aragonxpd154/8-bits-computer/ACC REGISTER/1.0V/PCB/PCB_PCB_ACC Register_2021-10-02.png

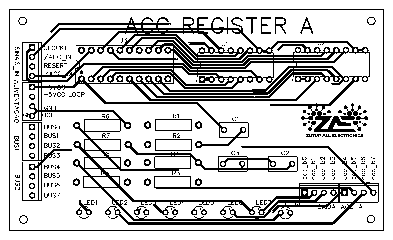
ACC REGISTER/1.0V/PCB/PCB_PCB_ACC Register_2021-10-02.png
