aragonxpd154/8-bits-computer/ACC REGISTER/2.0V/PCB/PCB_PCB_ACC Register 2.0V_2021-10-16.png

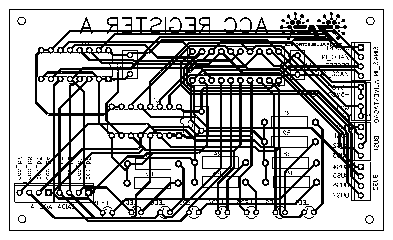
ACC REGISTER/2.0V/PCB/PCB_PCB_ACC Register 2.0V_2021-10-16.png
