aragonxpd154/8-bits-computer/ARITHMETIC LOGIC UNIT/1.0V/PCB/PCB_PCB_Arithmetic Logic Unit_2021-10-05.png

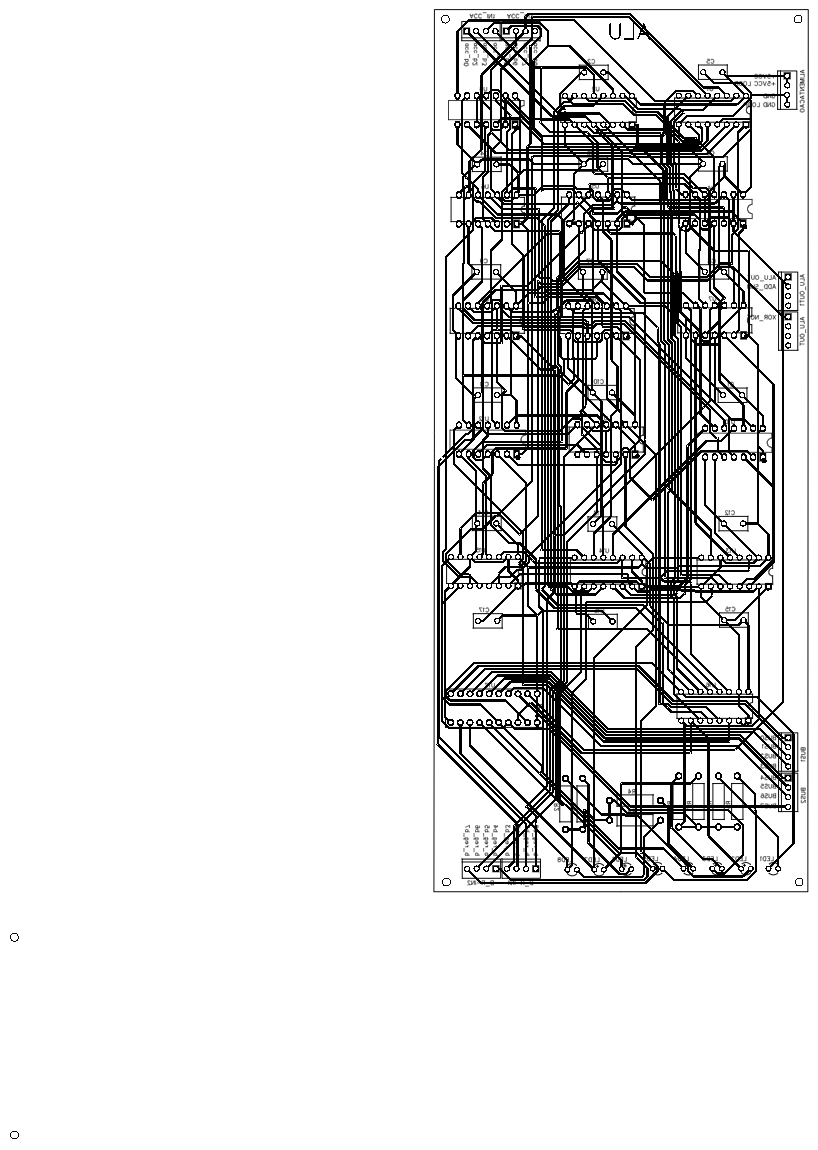
ARITHMETIC LOGIC UNIT/1.0V/PCB/PCB_PCB_Arithmetic Logic Unit_2021-10-05.png
