aragonxpd154/8-bits-computer/ASTABLE AND MONOSTABLE CLOCK CIRCUIT/1.0V/PCB/PCB_PCB_Astavel and Monostable Clock Circuit - 1.0V_2021-10-04.png

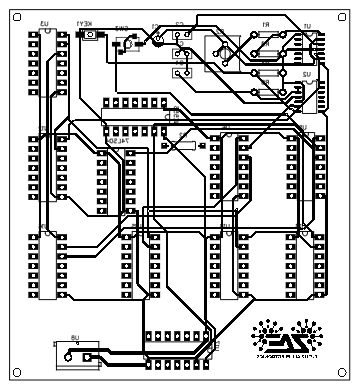
ASTABLE AND MONOSTABLE CLOCK CIRCUIT/1.0V/PCB/PCB_PCB_Astavel and Monostable Clock Circuit - 1.0V_2021-10-04.png
