aragonxpd154/8-bits-computer/DECIMAL DISPLAY/1.0V/PCB/PCB_PCB_Decimal Display_2021-10-08.png

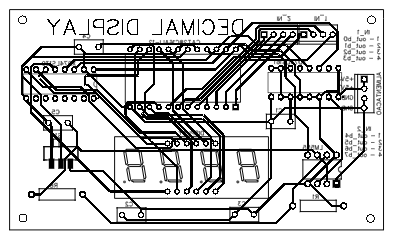
DECIMAL DISPLAY/1.0V/PCB/PCB_PCB_Decimal Display_2021-10-08.png
