aragonxpd154/8-bits-computer/OUTPUT REGISTER/1.0V/PCB/PCB_PCB_Output register_2021-10-31.png

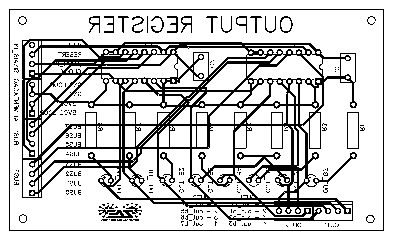
OUTPUT REGISTER/1.0V/PCB/PCB_PCB_Output register_2021-10-31.png
