aragonxpd154/8-bits-computer/PROGRAM COUNTER/1.0V/PCB/PCB_PCB_Program Counter - 1.0_2021-10-28.png

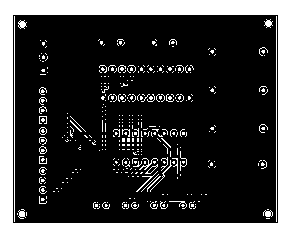
PROGRAM COUNTER/1.0V/PCB/PCB_PCB_Program Counter - 1.0_2021-10-28.png
