aragonxpd154/8-bits-computer/RAM & MAR/1.0V/PCB/PCB_PCB_RAM & MAR - 1.0_2021-12-04.png

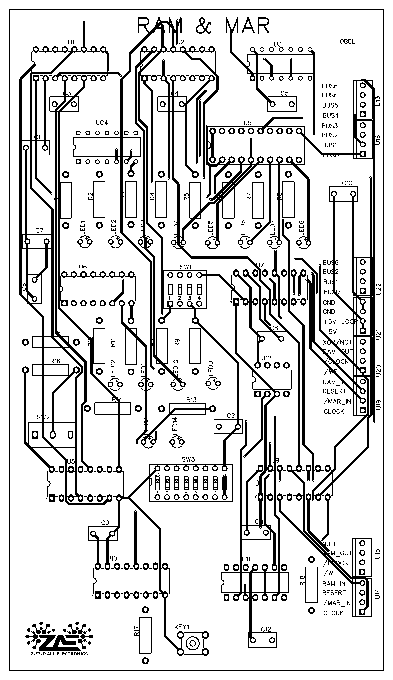
RAM & MAR/1.0V/PCB/PCB_PCB_RAM & MAR - 1.0_2021-12-04.png
