aragonxpd154/8-bits-computer/CONTROL DECODER/1.0V/PCB/BOM_PCB_Control Decoder_2021-12-04.csv

ID | Name | Designator | Footprint | Quantity | Manufacturer Part | Manufacturer | Supplier | Supplier Part | Price | Pins | 3DModel | JLCPCB Part Class | Contributor | link
1 | 100nF 63V poli7 | C1 | CAP-TH_L7.6-W3.8-P5.08-D0.51 | 1 | SR305C105KAR | AVX | LCSC | C444741 | 0.634 | 2 | CAP-TH_L7.6-W3.8-H7.6-P5.08 | Extended Part | LCSC | https://item.szlcsc.com/446097.html
2 | 100nF 63V poli | C2,C3 | CAP-TH_L7.6-W3.8-P5.08-D0.51 | 2 | SR305C105KAR | AVX | LCSC | C444741 | 0.634 | 2 | CAP-TH_L7.6-W3.8-H7.6-P5.08 | Extended Part | LCSC | https://item.szlcsc.com/446097.html
3 | CAT28C16AL-20 | U1,U2,U3 | DIP24-600 | 3 |  |  |  |  |  | 24
4 | SINAIS OUT | U4,U6,U7,U8,U9,U10,U11 | HDR-TH_4P-P2.54-D1.0 | 7 | 171825-4 | TE Connectivity | LCSC | C210162 | 0.156 | 4 | HDR-TH_4P-P2.54-D1.0 | Extended Part | 立创EDA官方封装库 | https://item.szlcsc.com/211174.html
5 | ALIM. | U5 | HDR-TH_4P-P2.54-D1.0 | 1 | 171825-4 | TE Connectivity | LCSC | C210162 | 0.156 | 4 | HDR-TH_4P-P2.54-D1.0 | Extended Part | 立创EDA官方封装库 | https://item.szlcsc.com/211174.html
