aragonxpd154/8-bits-computer/PROGRAM COUNTER/1.0V/PCB/BOM_PCB_Program Counter - 1.0_2021-10-28.csv

ID | Name | Designator | Footprint | Quantity | Manufacturer Part | Manufacturer | Supplier | Supplier Part | Price | Pins | 3DModel | JLCPCB Part Class | Contributor | description | link
1 | 100nF 63V | C1,C2 | CAP-TH_L7.6-W3.8-P5.08-D0.51 | 2 | SR305C105KAR | AVX | LCSC | C444741 | 0.402 | 2 | CAP-TH_L7.6-W3.8-H7.6-P5.08 | Extended Part | LCSC |  | https://item.szlcsc.com/446097.html
2 | VERDE | LED1,LED2,LED3,LED4 | LED-TH_BD3.0-P2.54-RD-GREEN | 4 | 264-7GD | Everlight Elec | LCSC | C605465 | 0.057 | 2 | LED-TH_BD3.0-P2.54-RD-GREEN | Extended Part | 立创EDA官方封装库 |  | https://atta.szlcsc.com/upload/public/pdf/source/20200615/C605465_1C0E18C6C0FE32F26DC47CD74F40D8BE.pdf
3 | 470 | R1,R2,R3,R4 | RES-TH_BD3.0-L9.5-P13.50-D0.6 | 4 | CFR02SJ0823A10 | UniOhm | LCSC | C69876 |  | 2 | RES-TH_BD3.0-L9.5-P13.50-D0.6 |  | 立创EDA官方封装库 |  | https://item.szlcsc.com/59631.html
4 | XD74LS161 | U1 | DIP-16_L19.2-W6.6-P2.54-LS7.6-BL | 1 | XD74LS161 | XINLUDA | LCSC | C609766 | 0.444 | 16 | DIP-16_L19.2-W6.6-H3.3-LS7.62-P2.54 | Extended Part | 立创EDA官方封装库 |  | https://item.szlcsc.com/82841.html
5 | SN74LS245N | U2 | DIP-20_L25.5-W10.0-P2.54-LS7.6-BL | 1 | SN74LS245N | Texas Instruments | LCSC | C352966 | 0.634 | 20 | DIP-20_L25.5-W10.0-H3.7-P2.54-LS7.6-BL | Extended Part | LCSC |  | https://item.szlcsc.com/398272.html
6 | SINAIS IN | U3 | HDR-TH_4P-P2.54-D1.0 | 1 | 171825-4 | TE Connectivity | LCSC | C210162 | 0.156 | 4 | HDR-TH_4P-P2.54-D1.0 | Extended Part | 立创EDA官方封装库 |  | https://item.szlcsc.com/211174.html
7 | 171825-4 | U4 | HDR-TH_4P-P2.54-D1.0 | 1 | 171825-4 | TE Connectivity | LCSC | C210162 | 0.156 | 4 | HDR-TH_4P-P2.54-D1.0 | Extended Part | 立创EDA官方封装库 |  | https://item.szlcsc.com/211174.html
8 | BUS | U5 | HDR-TH_4P-P2.54-D1.0 | 1 | 171825-4 | TE Connectivity | LCSC | C210162 | 0.156 | 4 | HDR-TH_4P-P2.54-D1.0 | Extended Part | 立创EDA官方封装库 |  | https://item.szlcsc.com/211174.html
9 | GS012-3.5-3P | U6 | H3-3.5-11.5X7.0MM | 1 | GS012-3.5-3P |  |  |  |  | 3 |  |  |  | DIP Screw Terminal;
