aragonxpd154/8-bits-computer/ASTABLE AND MONOSTABLE CLOCK CIRCUIT/2.0V/PCB/BOM_PCB_Astavel and Monostable Clock Circuit - 2.0_2021-10-20.csv

ID | Name | Designator | Footprint | Quantity | Manufacturer Part | Manufacturer | Supplier | Supplier Part | Price | Pins | 3DModel | JLCPCB Part Class | Contributor | Resistance(Ohms) | description | link
1 | 10uF 25V TANTALUM | C1 | CAP-TH_BD4.0-P1.50-D0.8-FD | 1 | SK100M035B070A | CapXon | LCSC | C62931 | 0.018 | 2 | CAP-TH_D4.0-H7.0-P1.5 | Extended Part | 官方封装库 |  |  | https://item.szlcsc.com/44342.html
2 | 10nF 63V poli | C2,C3 | CAP-TH_L5.5-W3.0-P5.00-D0.5 | 2 | 0.01uF(103) 100V | ReliaPro | LCSC | C10722 |  | 2 | CAP-TH_L5.5-W3.0-P5.00-D0.5 |  | 立创EDA官方封装库 |  |  | https://lcsc.com/product-detail/Polyester-Film-Capacitors_Made-in-China-0-01uF-103-100V_C10722.html
3 | 330nF 63V poli | C4 | CAP-TH_L5.5-W3.0-P5.00-D0.5 | 1 | 0.01uF(103) 100V | ReliaPro | LCSC | C10722 |  | 2 | CAP-TH_L5.5-W3.0-P5.00-D0.5 |  | 立创EDA官方封装库 |  |  | https://lcsc.com/product-detail/Polyester-Film-Capacitors_Made-in-China-0-01uF-103-100V_C10722.html
4 | 100nF 63V poli | C5,C6,C7 | CAP-TH_L5.5-W3.0-P5.00-D0.5 | 3 | 0.01uF(103) 100V | ReliaPro | LCSC | C10722 |  | 2 | CAP-TH_L5.5-W3.0-P5.00-D0.5 |  | 立创EDA官方封装库 |  |  | https://lcsc.com/product-detail/Polyester-Film-Capacitors_Made-in-China-0-01uF-103-100V_C10722.html
5 | VERDE | OUT | LED-TH_BD3.0-P2.54-RD-GREEN | 1 | 264-7GD | Everlight Elec | LCSC | C605465 | 0.057 | 2 | LED-TH_BD3.0-P2.54-RD-GREEN | Extended Part | 立创EDA官方封装库 |  |  | https://atta.szlcsc.com/upload/public/pdf/source/20200615/C605465_1C0E18C6C0FE32F26DC47CD74F40D8BE.pdf
6 | 150 | R1 | RES-TH_BD3.0-L9.5-P13.50-D0.6 | 1 | 7501/2w5% |  | LCSC | C48642 | 0.003 | 2 | RES-TH_BD3.0-L9.5-P13.50-D0.6 |  | 立创EDA官方封装库 |  |  | https://item.szlcsc.com/59631.html
7 | 10 | R2 | RES-TH_BD3.0-L9.5-P13.50-D0.6 | 1 | 7501/2w5% |  | LCSC | C48642 | 0.003 | 2 | RES-TH_BD3.0-L9.5-P13.50-D0.6 |  | 立创EDA官方封装库 |  |  | https://item.szlcsc.com/59631.html
8 | 10K | R4 | RES-TH_BD3.0-L9.5-P13.50-D0.6 | 1 | 7501/2w5% |  | LCSC | C48642 | 0.003 | 2 | RES-TH_BD3.0-L9.5-P13.50-D0.6 |  | 立创EDA官方封装库 |  |  | https://item.szlcsc.com/59631.html
9 | 330K | R5 | RES-TH_BD3.0-L9.5-P13.50-D0.6 | 1 | 7501/2w5% |  | LCSC | C48642 | 0.003 | 2 | RES-TH_BD3.0-L9.5-P13.50-D0.6 |  | 立创EDA官方封装库 |  |  | https://item.szlcsc.com/59631.html
10 | 470 | R6 | RES-TH_BD3.0-L9.5-P13.50-D0.6 | 1 | 7501/2w5% |  | LCSC | C48642 | 0.003 | 2 | RES-TH_BD3.0-L9.5-P13.50-D0.6 |  | 立创EDA官方封装库 |  |  | https://item.szlcsc.com/59631.html
11 | 100K LINEAR | AJT._FREQ | RES-ADJ-TH_3362P | 1 | 3362P-1-502LF | BOURNS | LCSC | C81260 | 0.203 | 3 | 3362P |  | 立创EDA官方封装库 | 5K |  | https://lcsc.com/product-detail/Precision-Potentiometer_Made-in-China-3362P-1-105_C20063.html
12 | SWITCH-SPDT | S1 | SWITCH-SPDT-SMD | 1 |  |  |  |  |  | 3 |  |  | SparkFun
13 | NE556N | NE556N | DIP-14_L19.0-W7.0-P2.54-LS7.6-BL | 1 | NE556N | TI | LCSC | C66175 | 0.343 | 14 | DIP-14_L19.0-W7.0-H3.5-LS7.62-P2.54 | Extended Part | 立创EDA官方封装库 |  |  | https://item.szlcsc.com/46313.html
14 | GS012-3.5-3P | U4,U5 | H3-3.5-11.5X7.0MM | 2 | GS012-3.5-3P |  |  |  |  | 3 |  |  |  |  | DIP Screw Terminal;
15 | button6*6*8.5 | CLOCK_MANUAL | KEY-TH_4P-L6.0-W6.0-P4.50 | 1 | button6*6*8.5 | ReliaPro | LCSC | C59980 | 0.017 | 4 | KEY-TH_4P-L6.0-W6.0-H4.3-LS6.5-P4.5 |  | 官方封装库 |  |  | https://lcsc.com/product-detail/Tactile-Switches_Made-in-China-Made-in-China-Made-in-China-Made-in-Cina-button6-6-8-5-Straight-line_C59980.html
16 | DM74LS04N | DM74LS04N | DIL-14 | 1 |  |  |  |  |  | 14 |  |  | keyboardjunkie
17 | XD74LS04 | 74LS00 | DIP-14_L19.4-W6.4-P2.54-LS7.6-BL | 1 | XD74LS04 | XINLUDA(信路达) | LCSC | C513524 | 0.234 | 14 | DIP-14_L19.4-W6.4-H5.3-P2.54-LS7.6-BL | Extended Part | LCSC |  |  | https://item.szlcsc.com/639765.html
