aragonxpd154/8-bits-computer/ASTABLE AND MONOSTABLE CLOCK CIRCUIT/1.0V/PCB/BOM_PCB_Astavel and Monostable Clock Circuit - 1.0V_2021-10-04.csv

EU IRIA | Nome | Designador | Pegada | Quantidade | Peça do Fabricante | Fabricante | Fornecedor | Peça do Fornecedor | Preço | Alfinetes | Contributor
1 | RTH025W | R2 | RTH025W | 1 |  |  |  |  |  | 2 | DangerousPrototype
2 | NE556DR | U1,U2 | SOIC-14_150MIL | 2 |  |  |  |  |  | 14
3 | 10 | R1 | AXIAL-0.3 | 1 |  |  |  |  |  | 2
4 | 100k | R2 | RES-ADJ_3386P | 1 |  |  |  |  |  | 3
5 | 10uF | C2 | RAD-0.1 | 1 |  |  |  |  |  | 2
6 | 10uF | C1 | CAP-D3.0XF1.5 | 1 |  |  |  |  |  | 2
7 | RS-285G05A2 | SW3 | KEY-6.0X3.6X2.5MM | 1 |  |  |  |  |  | 4
8 | 10k | R4 | AXIAL-0.3 | 1 |  |  |  |  |  | 2
9 | 150 | R3 | AXIAL-0.3 | 1 |  |  |  |  |  | 2
10 | Switch | KEY1 | KEY-3.0*4.0 | 1 |  |  |  |  |  | 2
11 | 10nF 63V Poliester | C3 | RAD-0.1 | 1 |  |  |  |  |  | 2
12 | 330nF 63V Poliester | C4 | RAD-0.1 | 1 |  |  |  |  |  | 2
13 | 330k | R5 | AXIAL-0.3 | 1 |  |  |  |  |  | 2
14 | 74LS00 | U3,U5,U6,U16 | 74LS04 DIP-14 | 4 |  |  |  |  |  | 14
15 | 74LS04 | U12,U13,U14,U15,U17,74LS04 | 74LS04 DIP-14 | 6 |  |  |  |  |  | 14
16 | NE556 | NE556 | 74LS04 DIP-14 | 1 |  |  |  |  |  | 14
17 | SCREWTERMINAL-5MM-2 | U8 | SCREWTERMINAL-5MM-2 | 1 |  |  |  |  |  | 2 | SparkFun
