aragonxpd154/8-bits-computer/PROGRAM COUNTER/3.0V/PCB/PCB_Program Counter - 3.0_2021-10-28.dxf

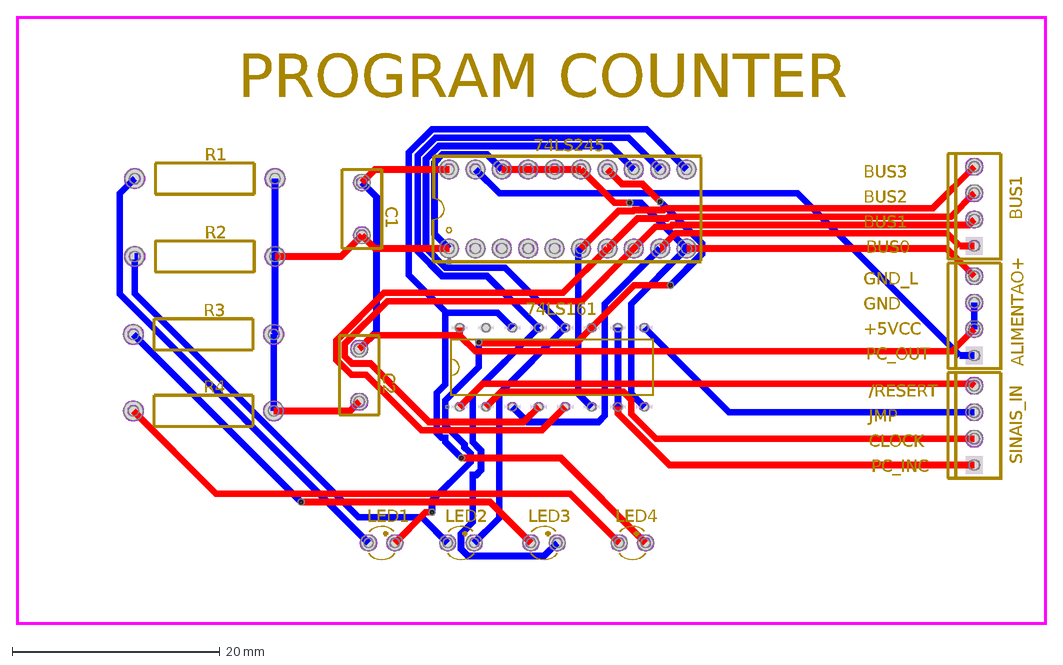
[picture p44: CAD file, 2021-10-28]
PROGRAM COUNTER/3.0V/PCB/PCB_Program Counter - 3.0_2021-10-28.dxf
PC_INC
CLOCK
JMP
/RESERT
PC_OUT
+5VCC
GND
GND_L
BUS0
BUS1
BUS2
BUS3
PROGRAM COUNTER
C1
C2
LED1
LED2
LED3
LED4
R1
R2
R3
R4
74LS161
74LS245
SINAIS_IN
ALIMENTAO+
