aragonxpd154/8-bits-computer/RAM & MAR/1.0V/PCB/PCB_RAM & MAR - 1.0_2021-12-04.dxf

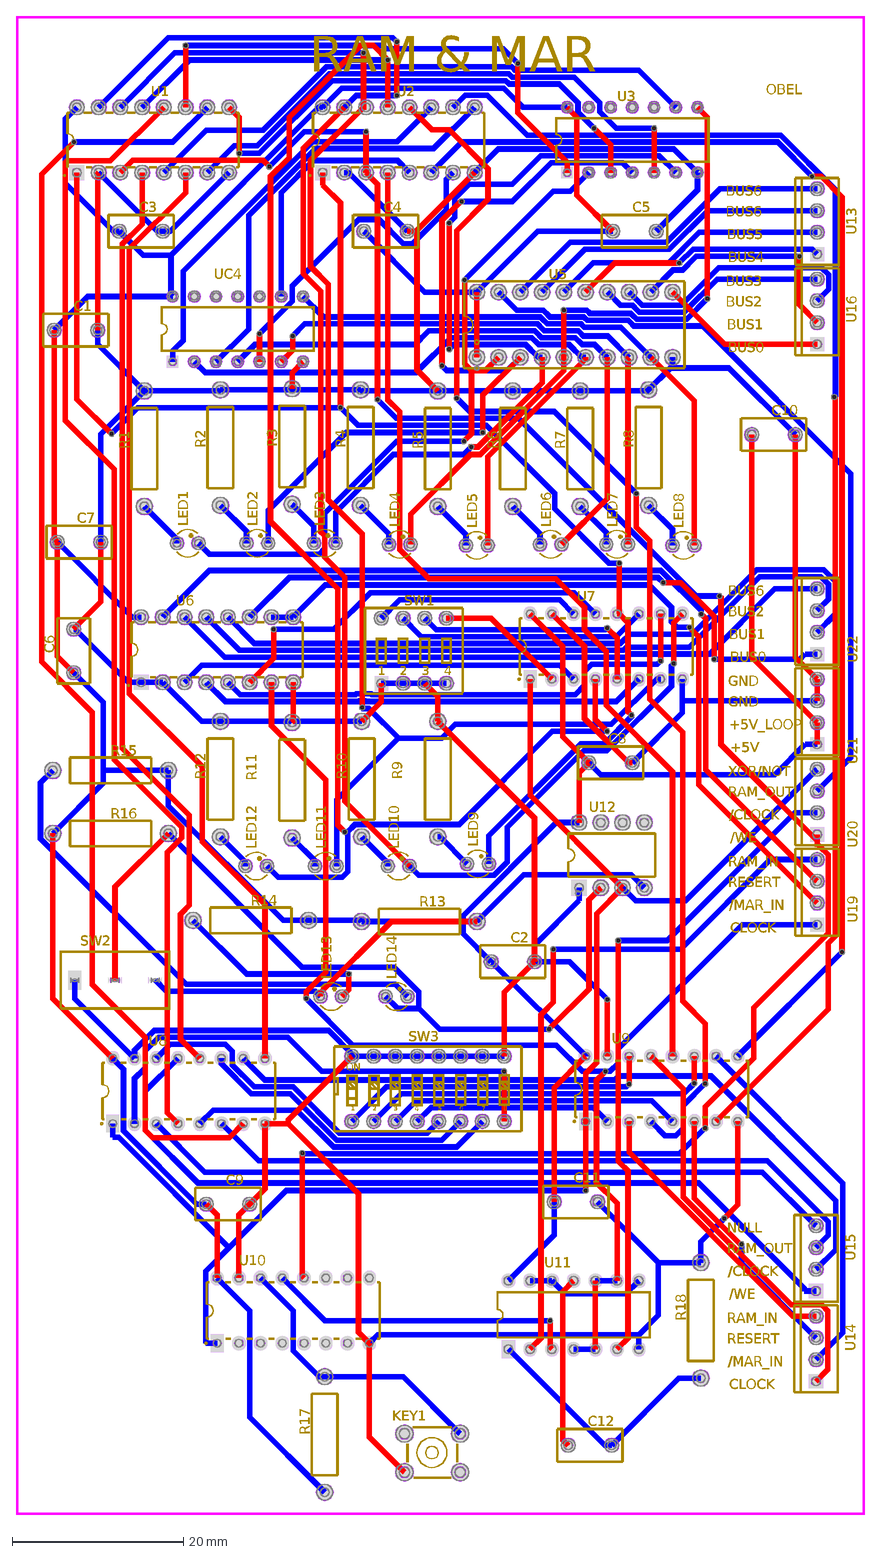
[picture p45: CAD file, 2021-12-04]
RAM & MAR/1.0V/PCB/PCB_RAM & MAR - 1.0_2021-12-04.dxf
OBEL
BUS3
BUS1
BUS0
BUS2
BUS6
BUS4
BUS5
GND
+5V
+5V_LOOP
XOR/NOT
/CLOCK
/WE
RAM_OUT
RESERT
CLOCK
/MAR_IN
RAM_IN
NULL
RAM & MAR
KEY1
LED1
LED2
LED3
LED4
LED5
LED6
LED7
LED8
LED9
LED10
LED11
LED12
LED13
LED14
SW1
1
2
3
4
SW2
SW3
ON
5
6
7
8
U1
U2
U3
U5
U6
U7
U8
U9
U10
U11
U12
U13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
