aragonxpd154/8-bits-computer/INSTRUCTION REGISTER/2.0V/PCB/PCB_PCB_Instruction Register 2.0V_2021-10-21.png

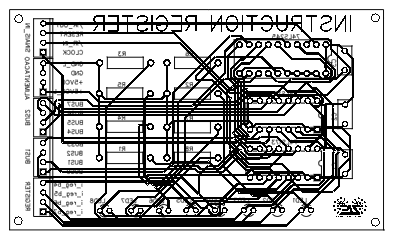
INSTRUCTION REGISTER/2.0V/PCB/PCB_PCB_Instruction Register 2.0V_2021-10-21.png
