aragonxpd154/8-bits-computer/ASTABLE AND MONOSTABLE CLOCK CIRCUIT/1.0V/Schematic_Astavel and Monostable Clock Circuit_2021-10-04.pdf

# U7.1GND

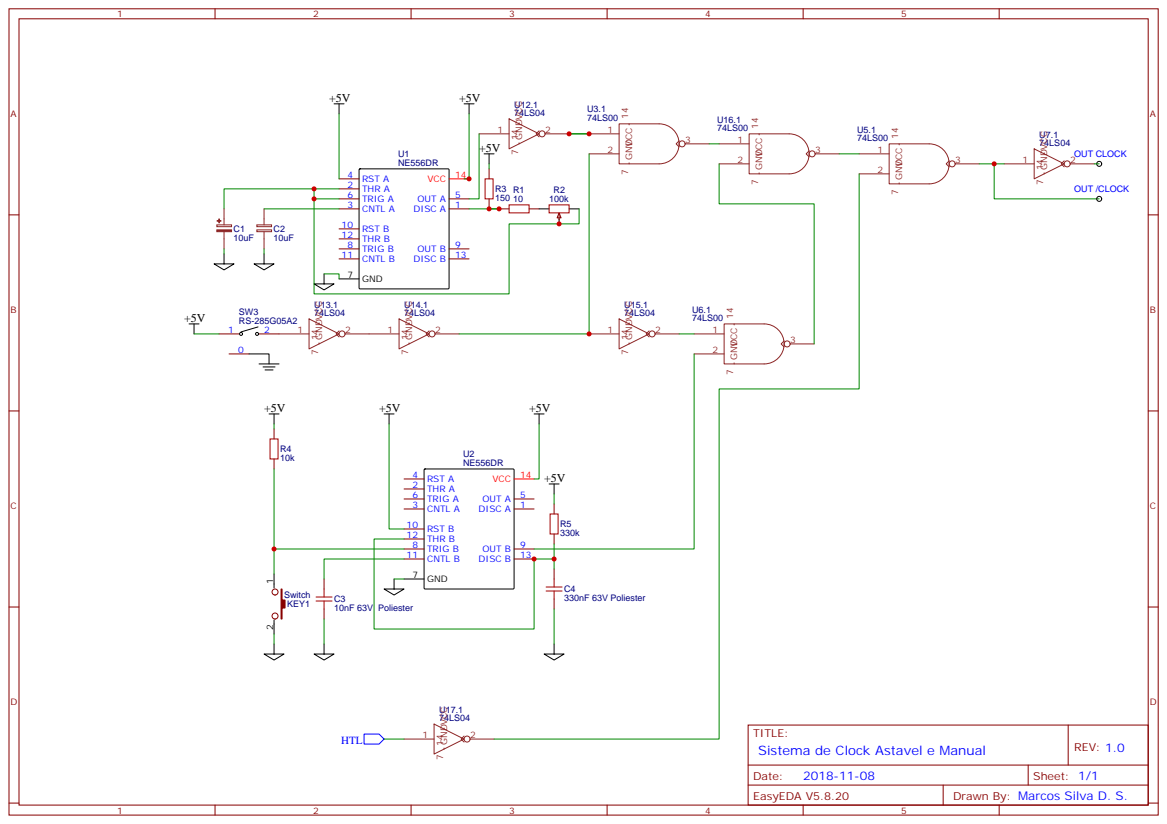
[picture p59: page 1]

TITLE:
Sistema de Clock Astavel e Manual
