aragonxpd154/8-bits-computer/ARITHMETIC LOGIC UNIT/1.0V/Schematic_Arithmetic Logic Unit_2021-10-03.pdf

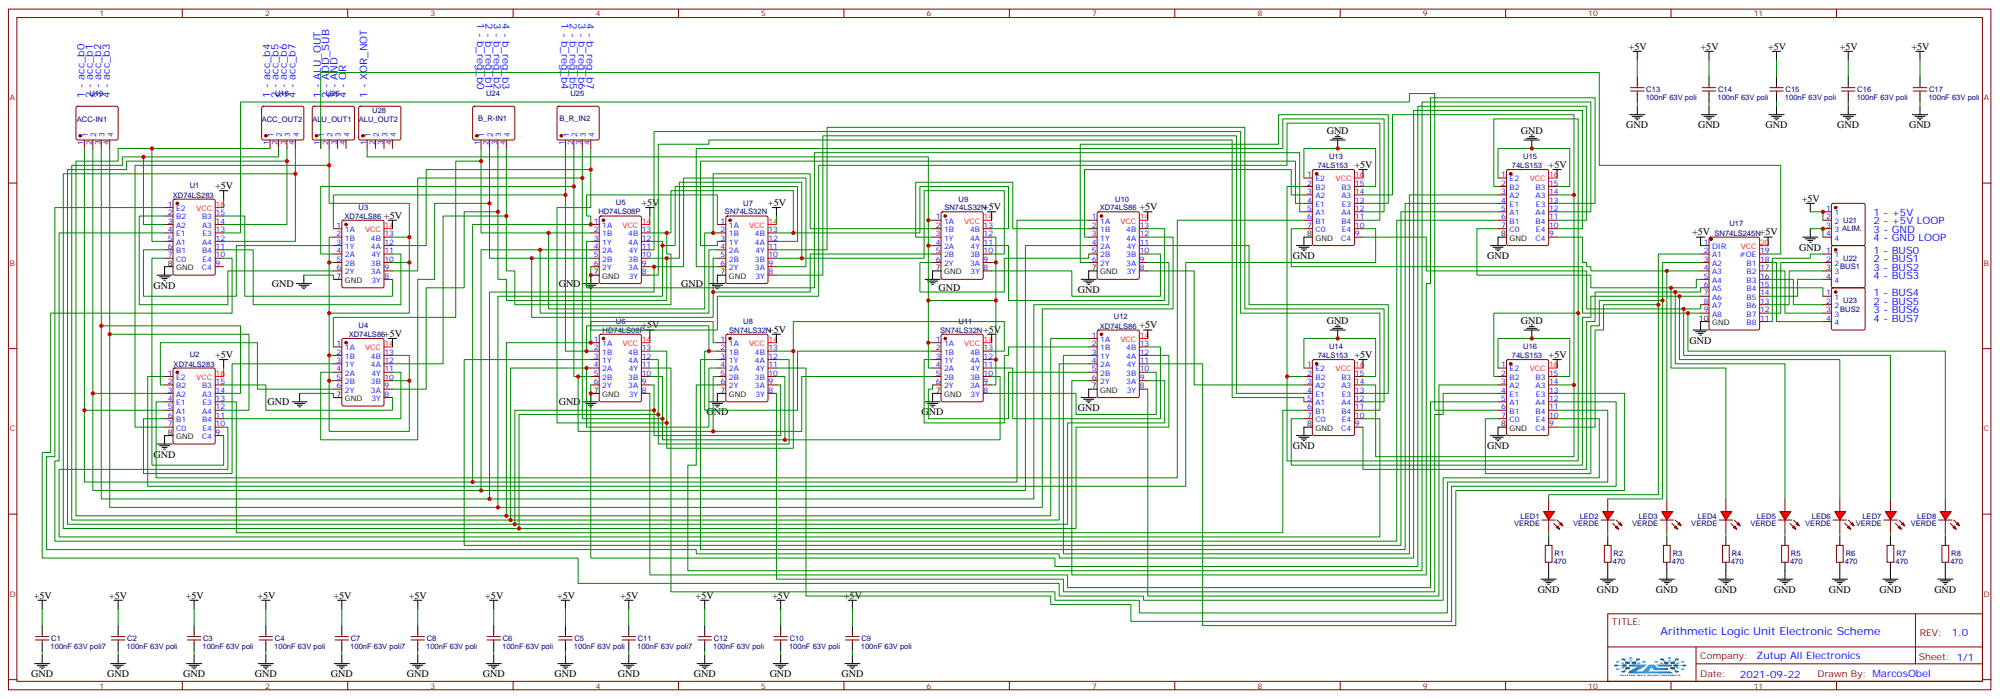
[picture p60: page 1]

4 13
5 12
6 11

Company: Zutup All Electronics
