aragonxpd154/8-bits-computer/ACC REGISTER/1.0V/Schematic_ACC Register_2021-10-02.pdf

# G2# 10 4D 11 3D 12 2D 13 1D 14 CLR 15 VCC 16

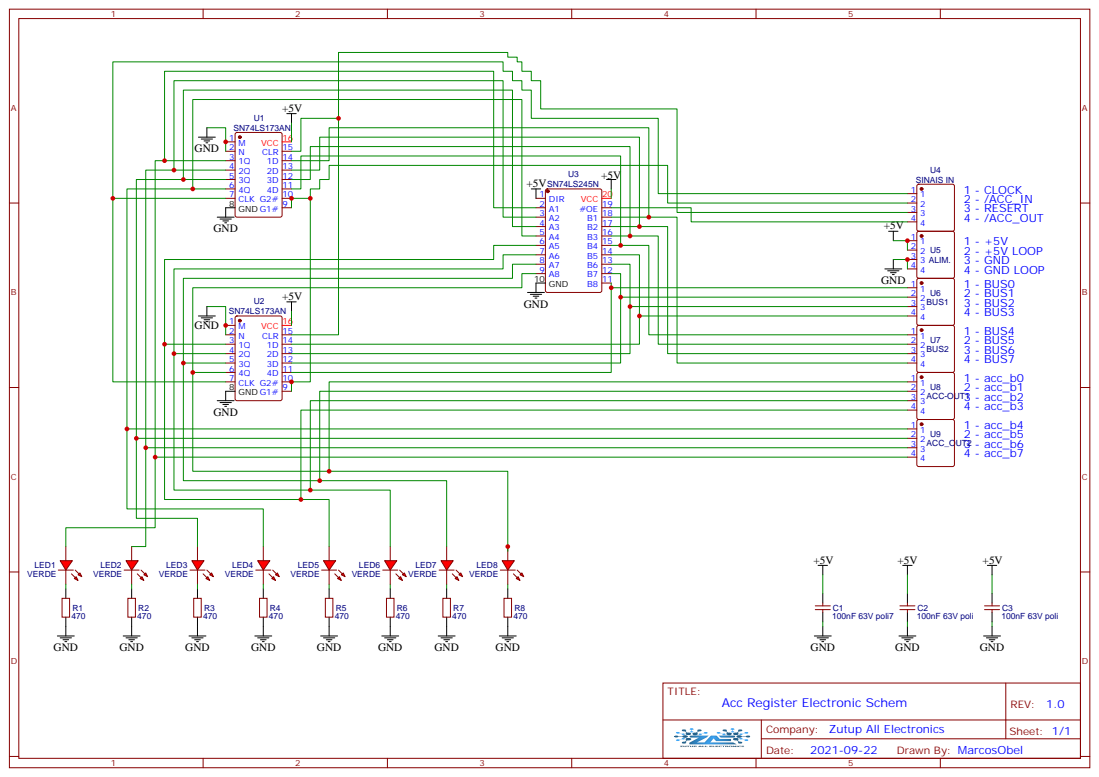
[picture p61: page 1]

Company: Zutup All Electronics
