aragonxpd154/8-bits-computer/INSTRUCTION REGISTER/1.0V/PCB/PCB_PCB_Instruction Register 1.0V_2021-10-21.pdf

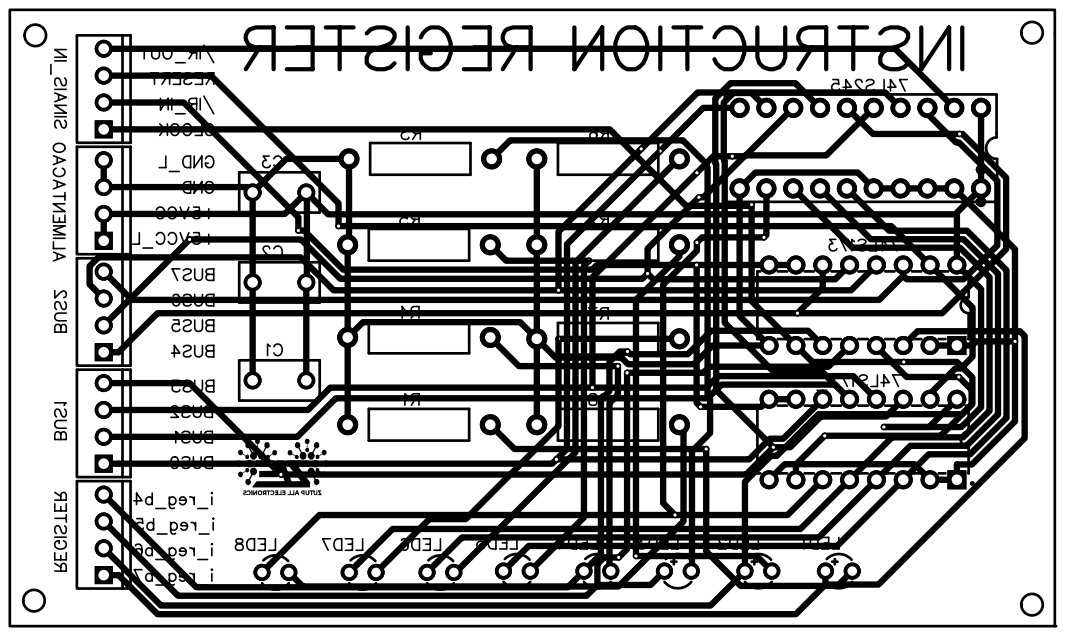
[picture p62: page 1]
