aragonxpd154/8-bits-computer/CONTROL DECODER/1.0V/PCB/PCB_PCB_Control Decoder_2021-12-04.pdf

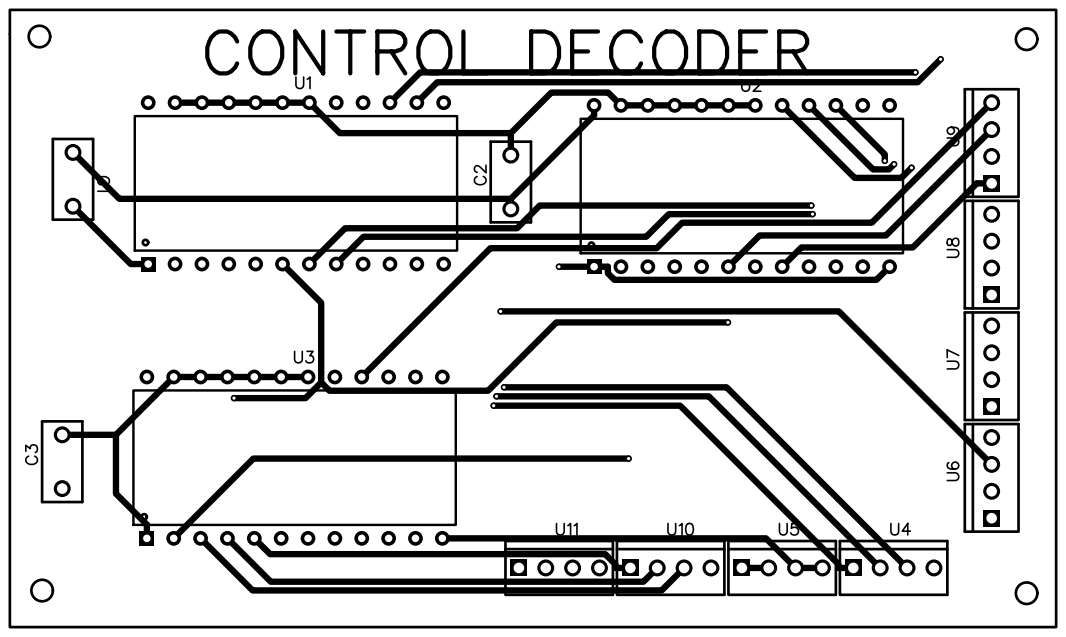
[picture p63: page 1]
