aragonxpd154/8-bits-computer/PROGRAM COUNTER/2.0V/PCB/PCB_PCB_Program Counter - 2.0_2021-10-28.pdf

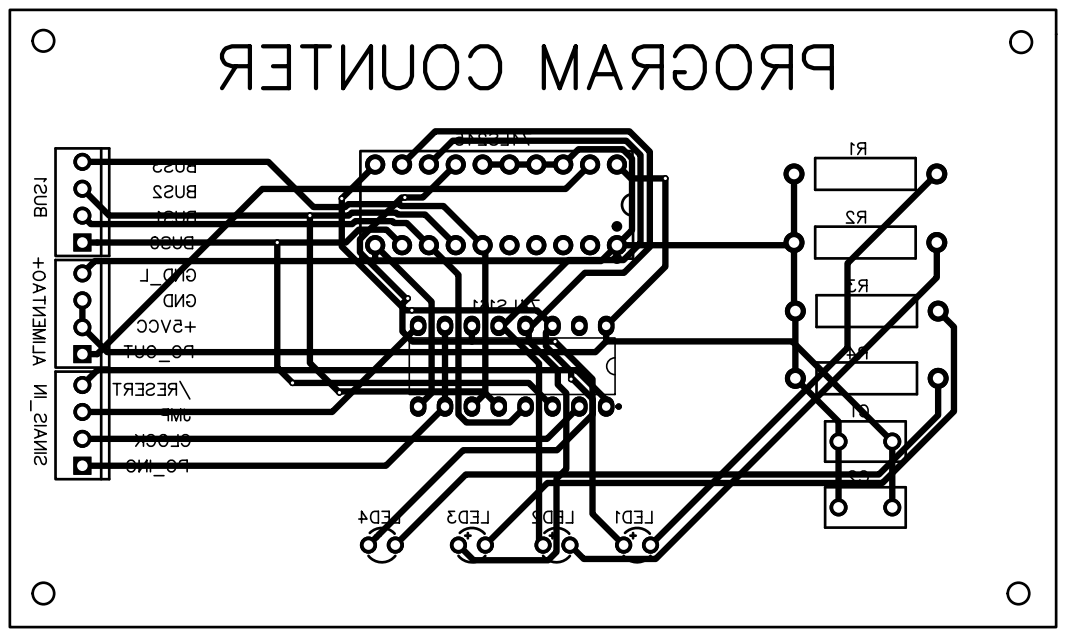
[picture p67: page 1]
