aragonxpd154/8-bits-computer/PROGRAM COUNTER/1.0V/PCB/PCB_PCB_Program Counter - 1.0_2021-10-28.pdf

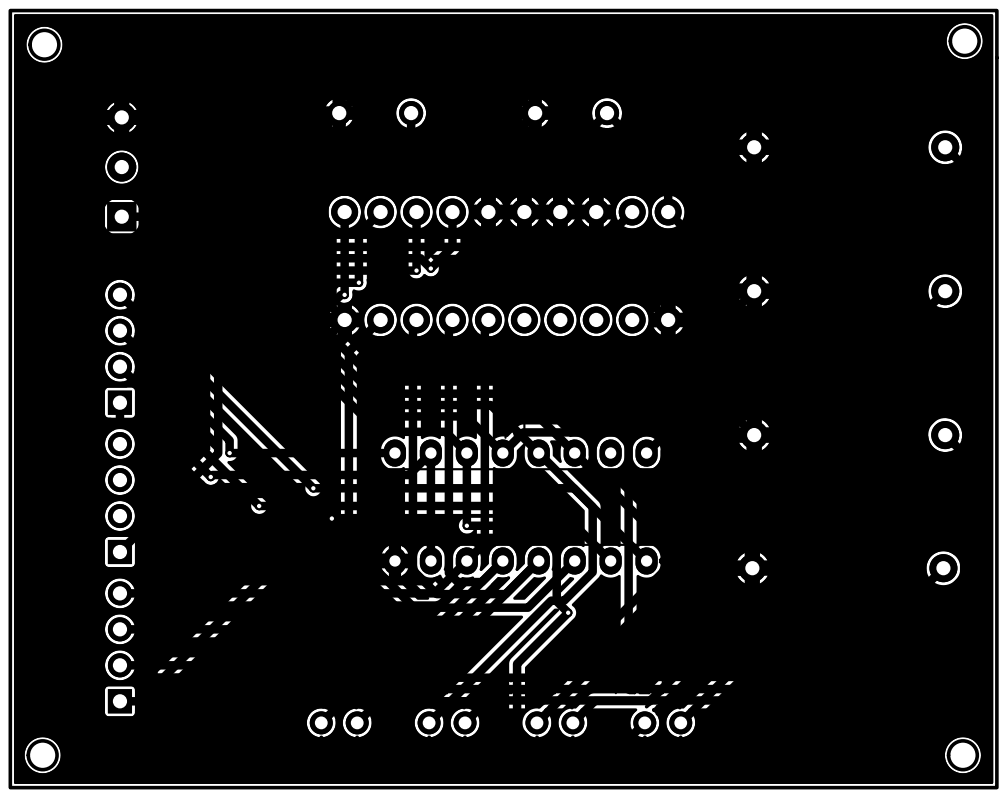
[picture p68: page 1]
