aragonxpd154/8-bits-computer/ASTABLE AND MONOSTABLE CLOCK CIRCUIT/2.1V/PCB/PCB_PCB_Astavel and Monostable Clock Circuit - 2.1_2021-10-20.pdf

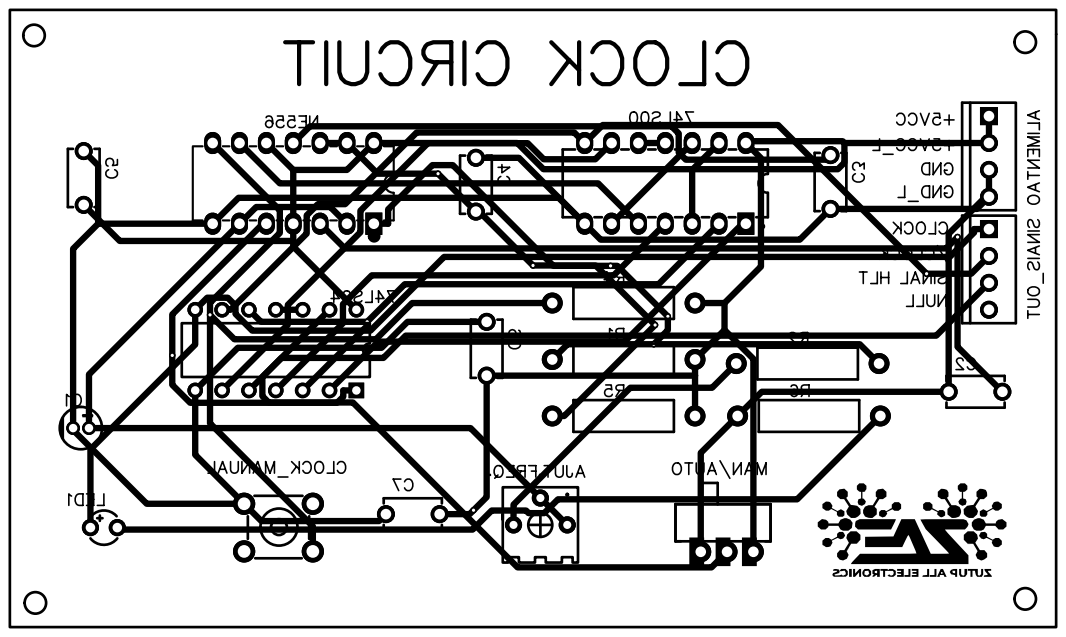
[picture p69: page 1]
