aragonxpd154/8-bits-computer/ASTABLE AND MONOSTABLE CLOCK CIRCUIT/2.0V/PCB/PCB_PCB_Astavel and Monostable Clock Circuit - 2.0_2021-10-20.pdf

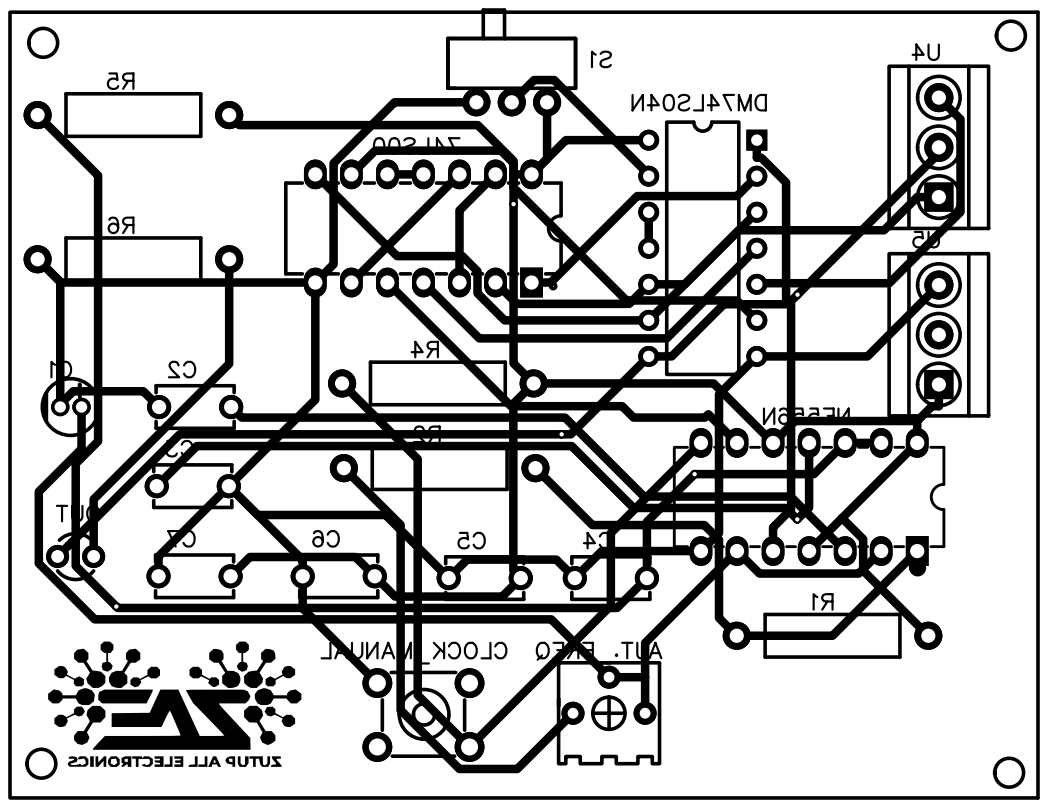
[picture p70: page 1]
