aragonxpd154/8-bits-computer/B REGISTER/2.0V/PCB/PCB_PCB_B Register 2.0V_2021-10-13.pdf

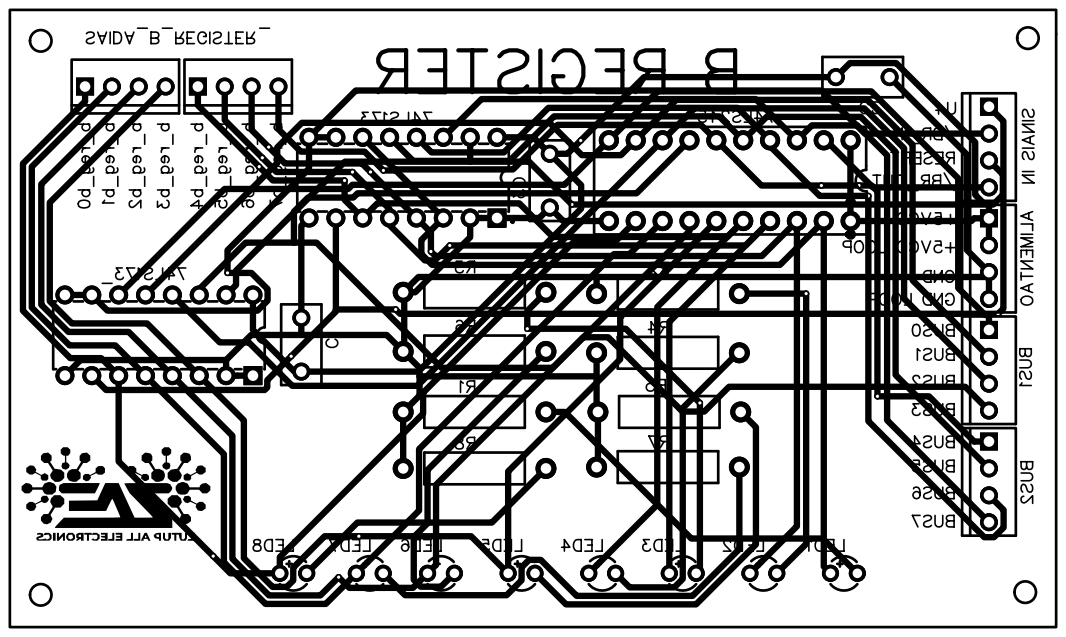
[picture p72: page 1]
