aragonxpd154/8-bits-computer/FETCH EXECUTION COUNTER/1.0V/PCB/PCB_PCB_Fetch Execution Counter_2021-10-12.pdf

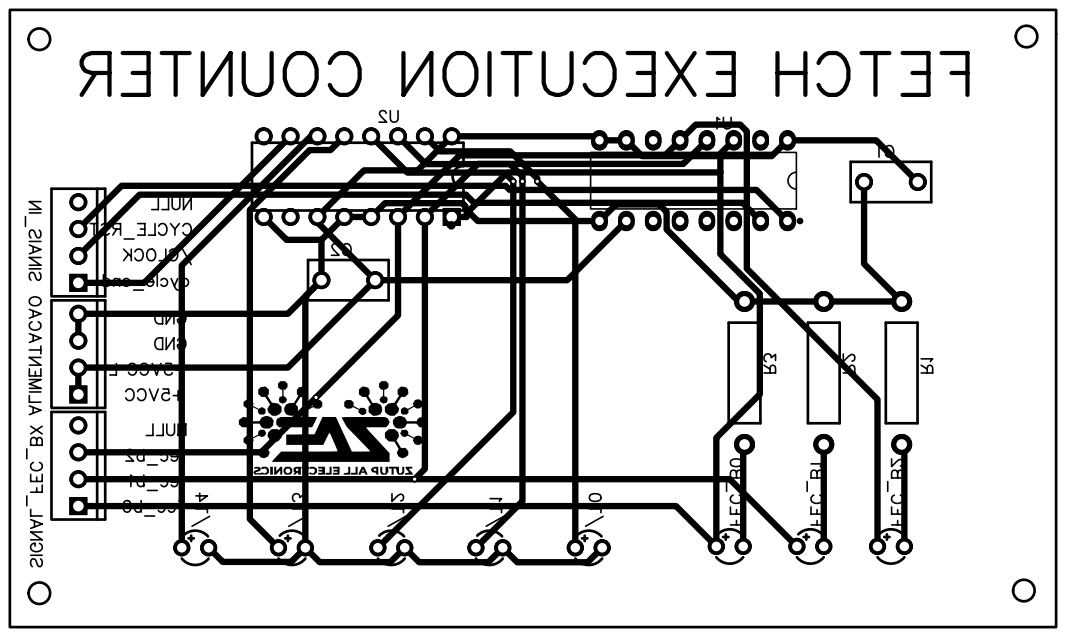
[picture p73: page 1]
