aragonxpd154/8-bits-computer/B REGISTER/1.0V/PCB/PCB_PCB_B Register_2021-10-06.pdf

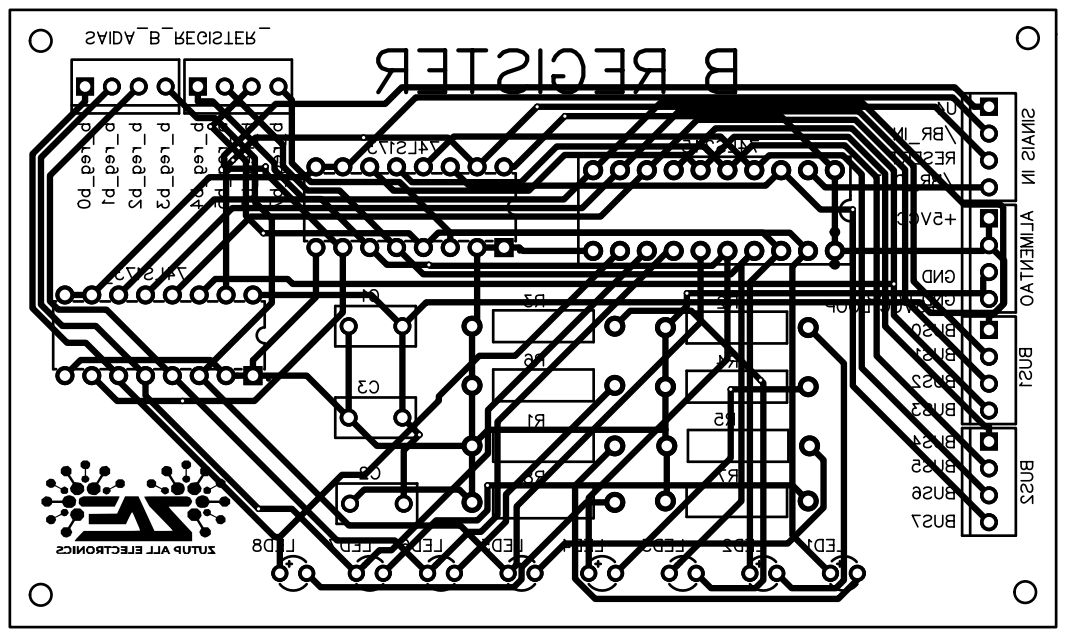
[picture p75: page 1]
