aragonxpd154/8-bits-computer/~REHEARSAL~/ASTABLE AND MONSTABLE CLOCK CIRCUIT/2.0V/CIRCUIT TEST IN PCB/PHOTOS/IMG_20211019_081933683.jpg

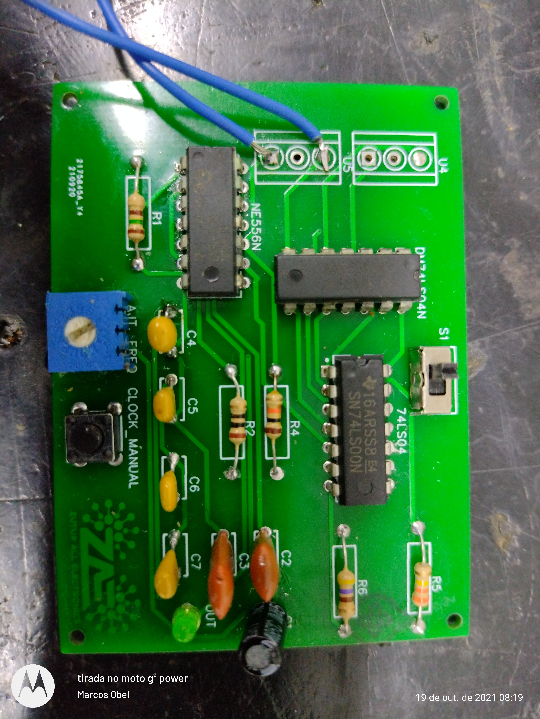
~REHEARSAL~/ASTABLE AND MONSTABLE CLOCK CIRCUIT/2.0V/CIRCUIT TEST IN PCB/PHOTOS/IMG_20211019_081933683.jpg
